WithanagePerera/M.2-Accelerator/DDR3L Pin Mapping Images/Image 1.png

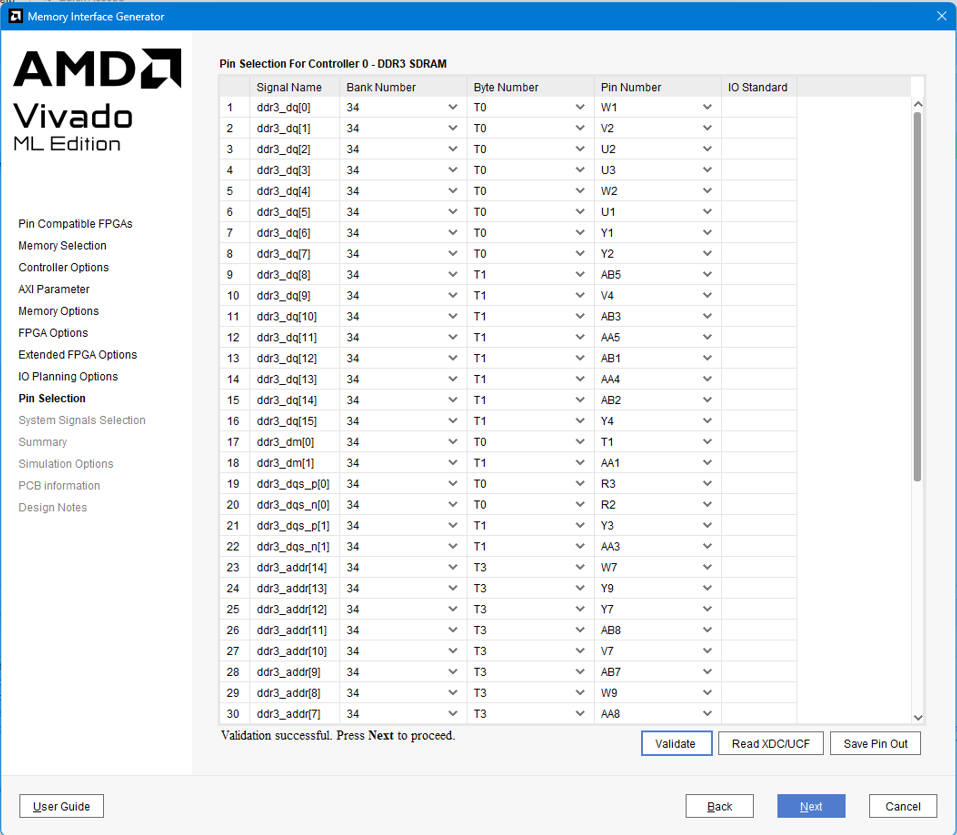
DDR3L Pin Mapping Images/Image 1.png
