WithanagePerera/M.2-Accelerator/DDR3L Pin Mapping Images/Image 2.png

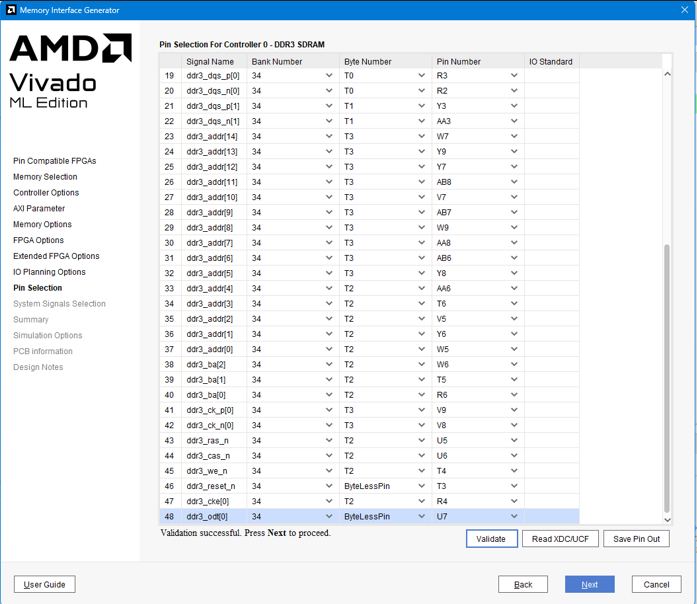
DDR3L Pin Mapping Images/Image 2.png
